LiamDGray/LightBoard2x2/Photos of Chinese product/Chinese 2x2 housing side.jpg

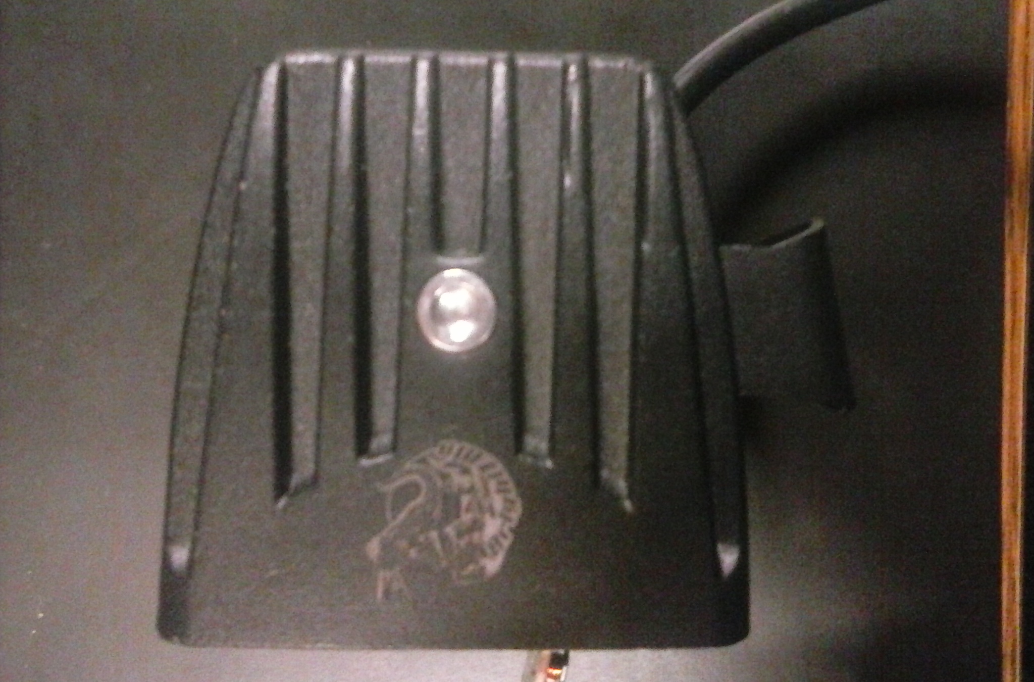
Photos of Chinese product/Chinese 2x2 housing side.jpg
