LiamDGray/LightBoard2x2/Photos of Chinese product/Reflector.JPG

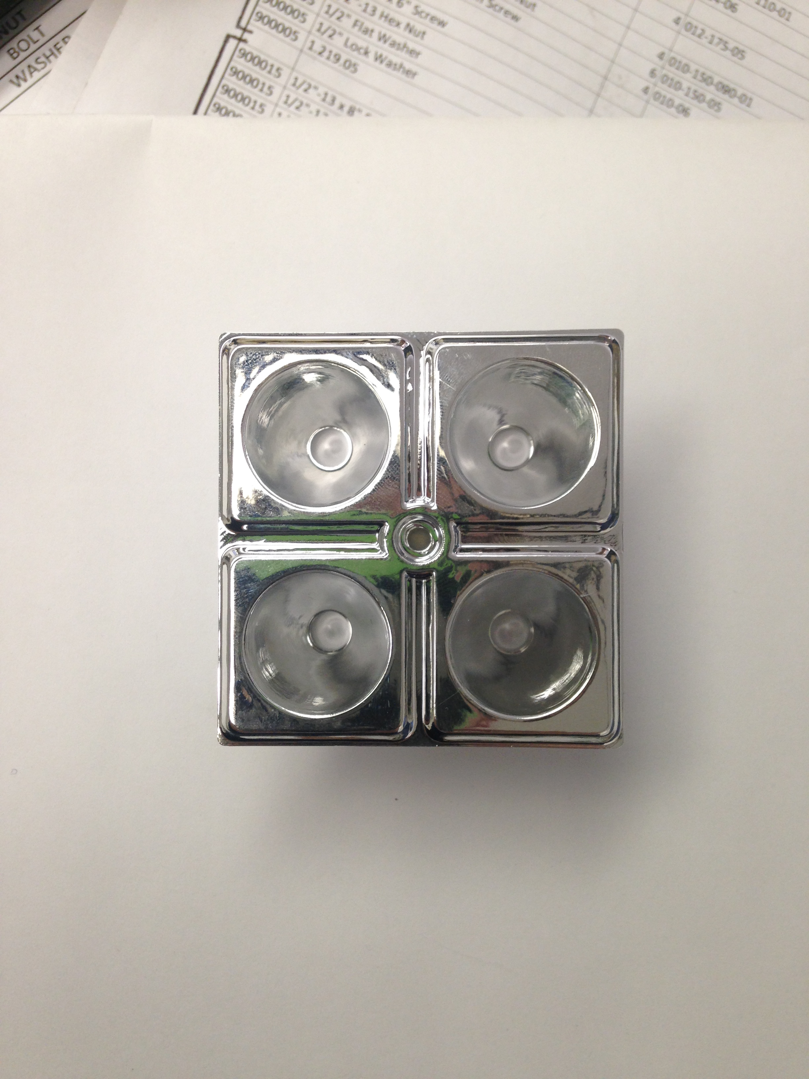
Photos of Chinese product/Reflector.JPG
